randika-perera/High-Frequency-Amplifier/Images/Breadboard Implemention Side View.jpg

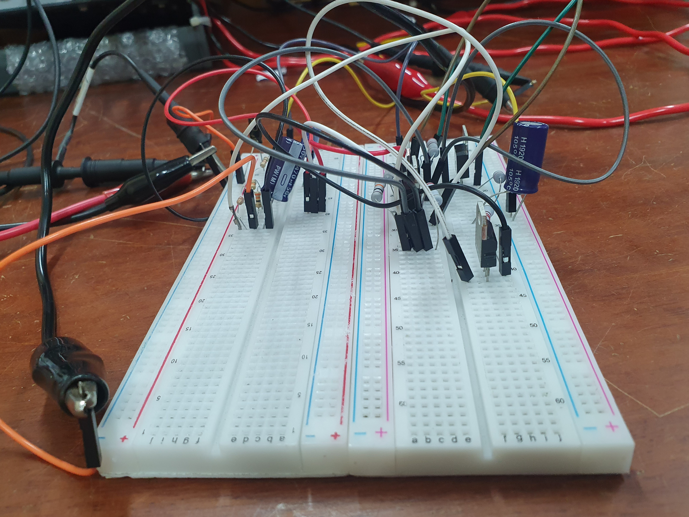
Images/Breadboard Implemention Side View.jpg
