randika-perera/High-Frequency-Amplifier/Images/Circuit Board Side View.jpg

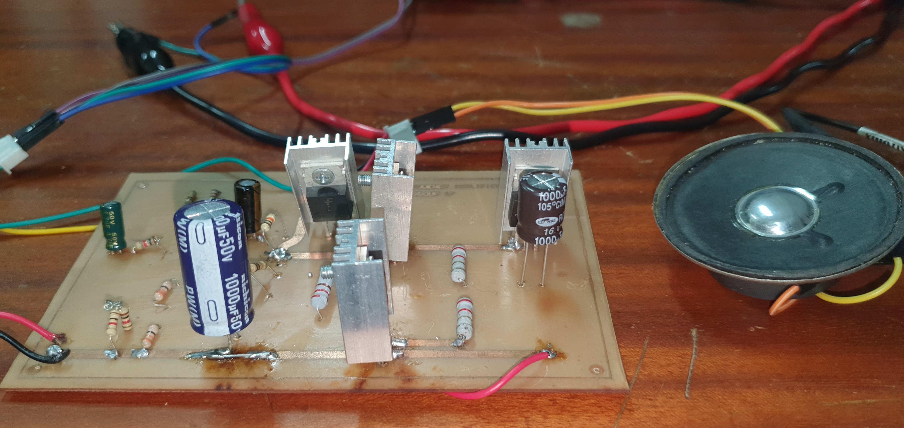
Images/Circuit Board Side View.jpg
