randika-perera/High-Frequency-Amplifier/Images/Enclosure.jpg

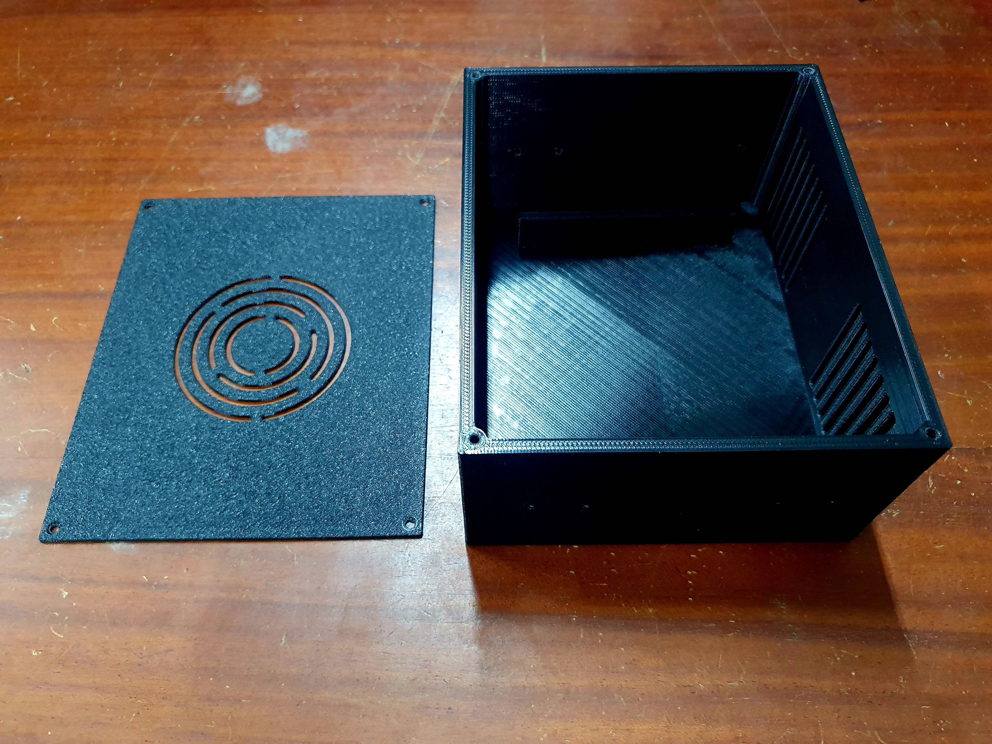
Images/Enclosure.jpg
