randika-perera/High-Frequency-Amplifier/Images/Final PCB 3D View.jpg

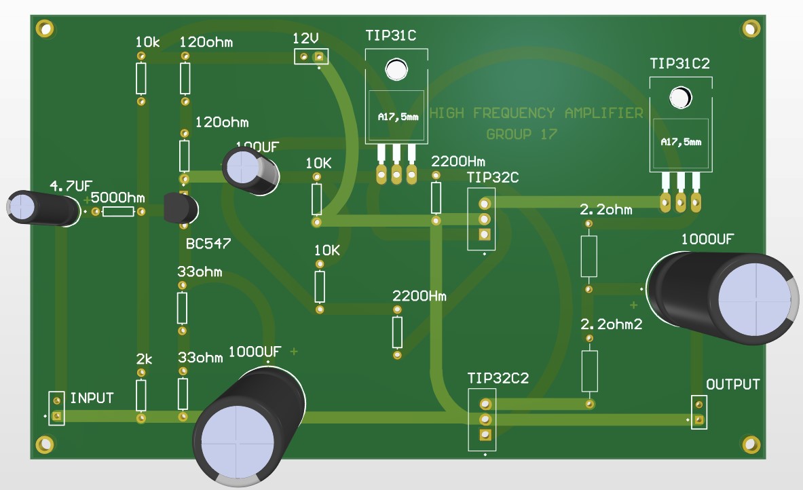
Images/Final PCB 3D View.jpg
