randika-perera/High-Frequency-Amplifier/Images/Final PCB.jpg

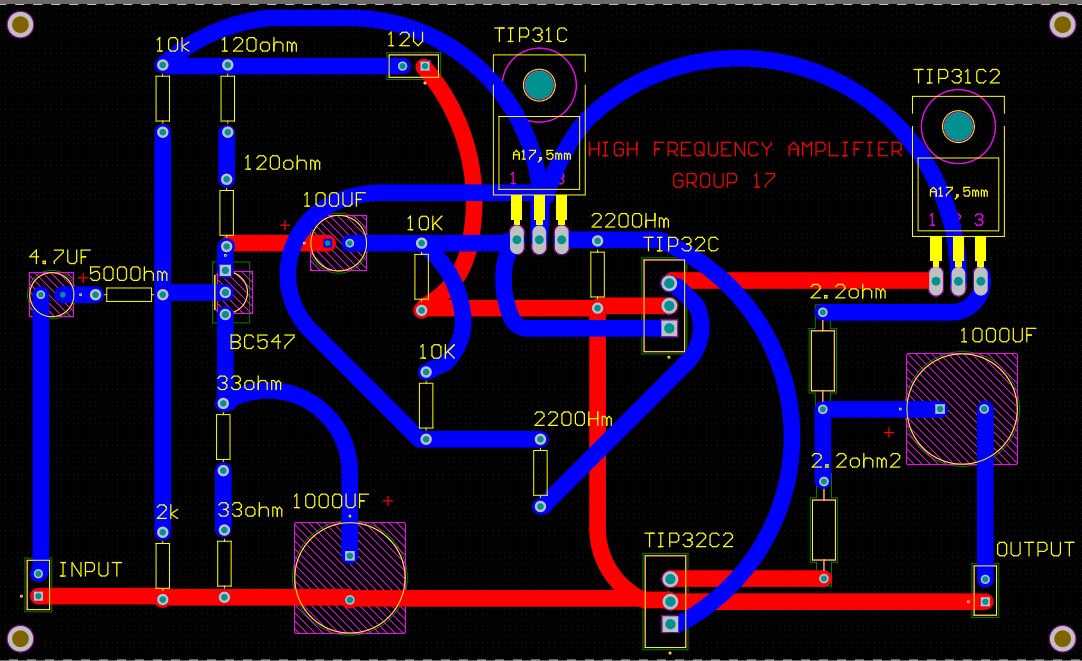
Images/Final PCB.jpg
