randika-perera/High-Frequency-Amplifier/Images/Final Project Rear View.jpg

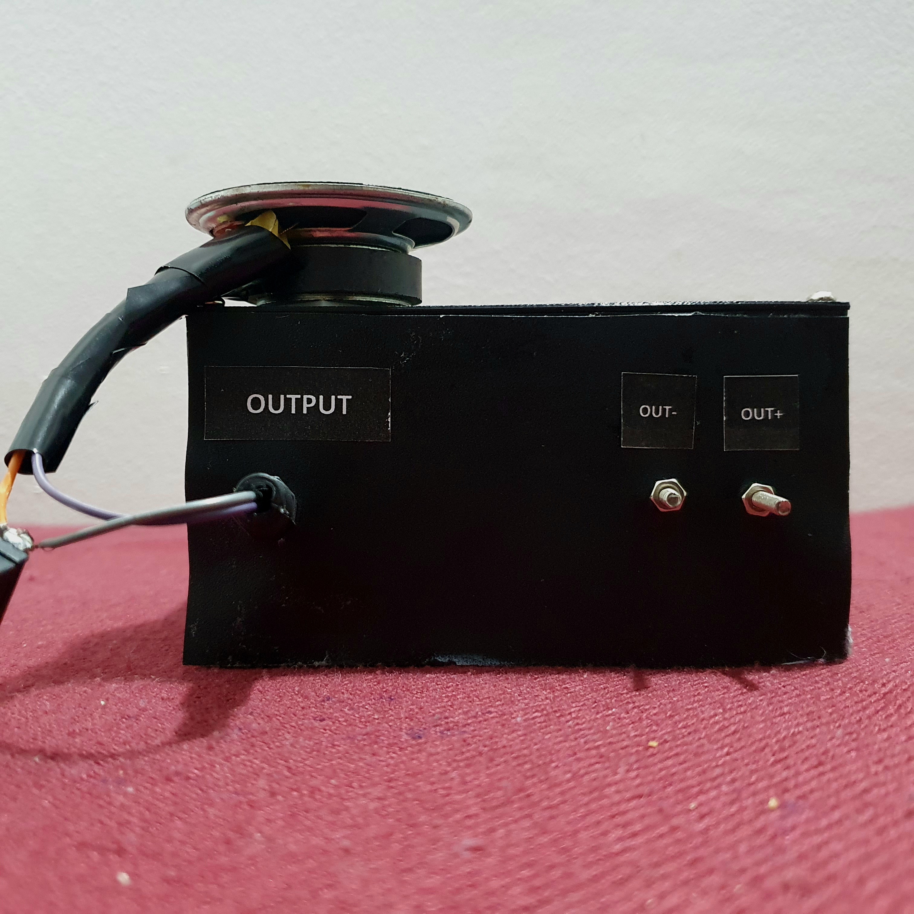
Images/Final Project Rear View.jpg
