randika-perera/High-Frequency-Amplifier/Images/Oscilloscope Open Circuit 20kHz.jpg

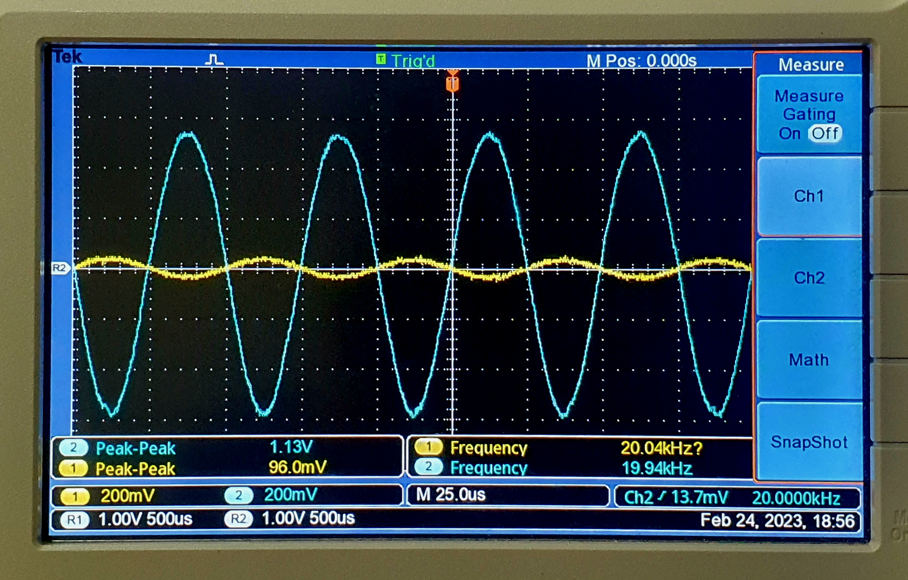
Images/Oscilloscope Open Circuit 20kHz.jpg
