randika-perera/High-Frequency-Amplifier/PCB Desgin/Images/SINGLE_LAYER.jpg

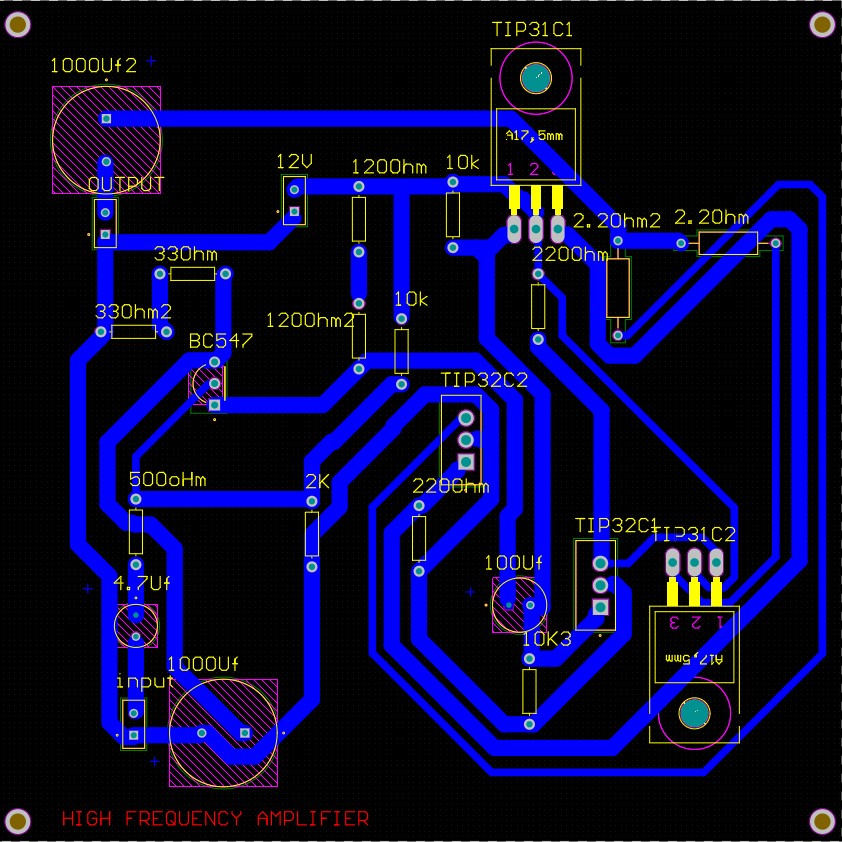
PCB Desgin/Images/SINGLE_LAYER.jpg
