randika-perera/High-Frequency-Amplifier/PCB Desgin/Images/TOPCOPPER.jpg

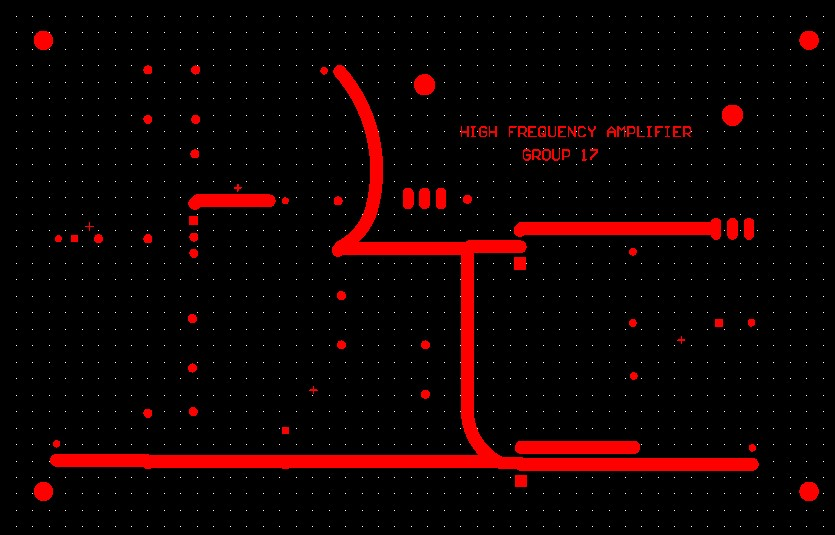
PCB Desgin/Images/TOPCOPPER.jpg
